squiggles1024/FitnessController/CAD Models/12mm-button-without-cap-with-round-square-cap-1.snapshot.3/12mmx12mm With White cap round.stp

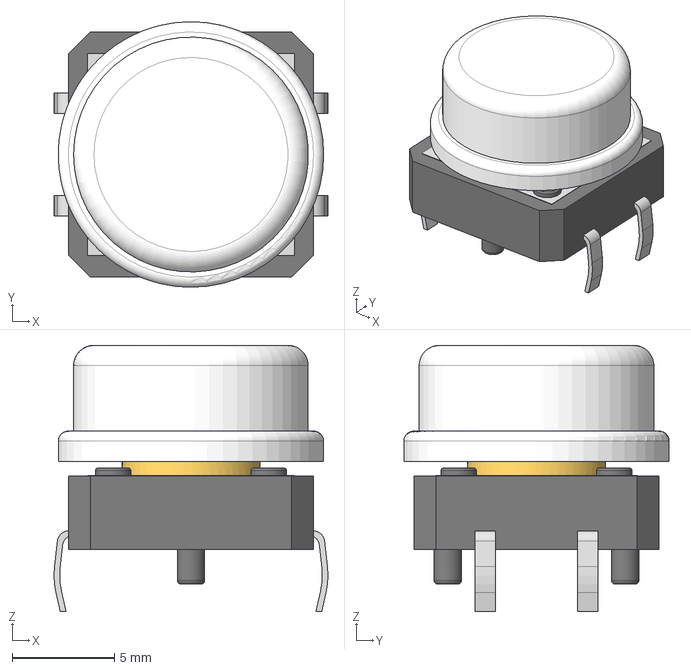
[picture p21: CAD file, 2022-12-01]
CAD Models/12mm-button-without-cap-with-round-square-cap-1.snapshot.3/12mmx12mm With White cap round.stp
13.4 x 13.0 x 13.0 mm
