squiggles1024/FitnessController/CAD Models/Trigger.SLDPRT

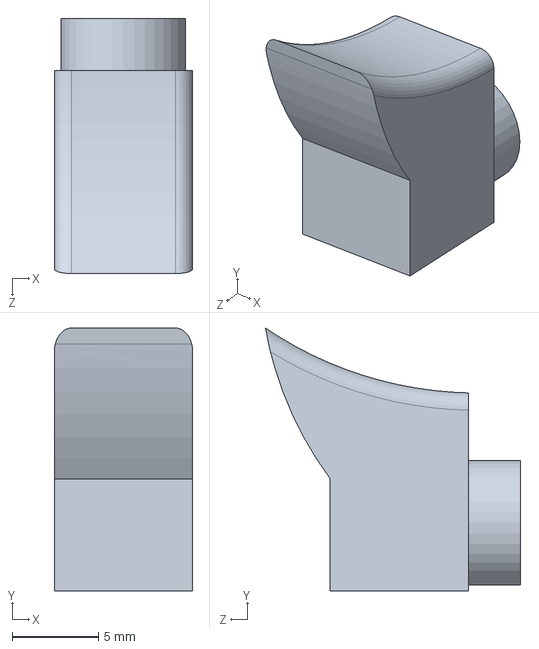
[picture p25: CAD file, 2022-12-01]
CAD Models/Trigger.SLDPRT
8.00 x 15.2 x 14.7 mm
