squiggles1024/FitnessController/CAD Models/NunChuck_Top.SLDPRT

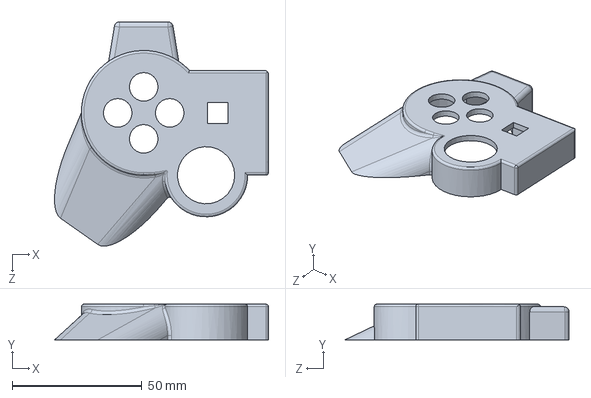
[picture p26: CAD file, 2022-12-01]
CAD Models/NunChuck_Top.SLDPRT
82.3 x 13.8 x 86.3 mm
