squiggles1024/FitnessController/CAD Models/12mm-button-without-cap-with-round-square-cap-1.snapshot.3/12mmx12mm Without cap.stp

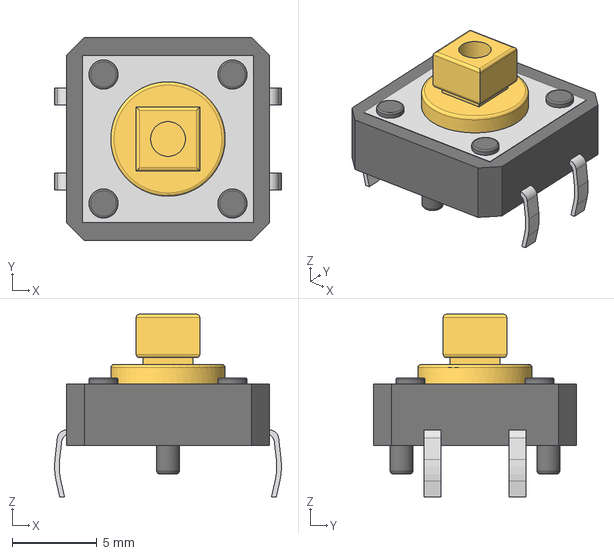
[picture p29: CAD file, 2022-12-01]
CAD Models/12mm-button-without-cap-with-round-square-cap-1.snapshot.3/12mmx12mm Without cap.stp
13.4 x 12.0 x 10.8 mm
