squiggles1024/FitnessController/CAD Models/tactile-switch-thru-6mm-series-1.snapshot.25/Tactal Switch -Thru (6mmx 6mmx4.5mm).stp

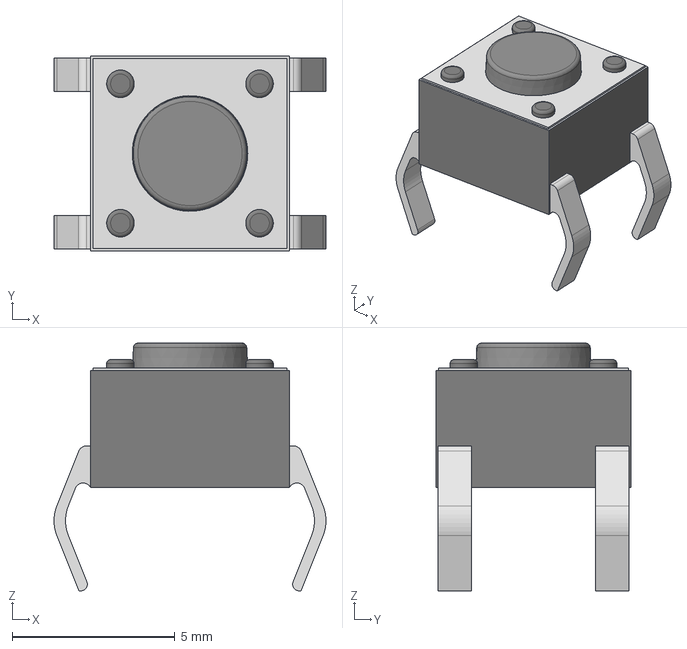
[picture p30: CAD file, 2022-12-01]
CAD Models/tactile-switch-thru-6mm-series-1.snapshot.25/Tactal Switch -Thru (6mmx 6mmx4.5mm).stp
8.37 x 5.99 x 7.62 mm
