squiggles1024/FitnessController/Core/Src/gpio.c

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

/* Includes ------------------------------------------------------------------*/
#include "gpio.h"

/*----------------------------------------------------------------------------*/
/* Configure GPIO                                                             */
/*----------------------------------------------------------------------------*/
/** Configure pins as
        * Analog
        * Input
        * Output
        * EVENT_OUT
        * EXTI
     PA9   ------> USB_OTG_FS_VBUS
     PA10   ------> USB_OTG_FS_ID
     PA11   ------> USB_OTG_FS_DM
     PA12   ------> USB_OTG_FS_DP
*/
void MX_GPIO_Init(void)
{

  GPIO_InitTypeDef GPIO_InitStruct = {0};

  /* GPIO Ports Clock Enable */
  __HAL_RCC_GPIOE_CLK_ENABLE();
  __HAL_RCC_GPIOC_CLK_ENABLE();
  __HAL_RCC_GPIOA_CLK_ENABLE();
  __HAL_RCC_GPIOB_CLK_ENABLE();
  __HAL_RCC_GPIOD_CLK_ENABLE();

  /*Configure GPIO pin Output Level */
  HAL_GPIO_WritePin(LED2_GPIO_Port, LED2_Pin, GPIO_PIN_RESET);

  /*Configure GPIO pin Output Level */
  HAL_GPIO_WritePin(SPBTLE_RF_SPI3_CSN_GPIO_Port, SPBTLE_RF_SPI3_CSN_Pin, GPIO_PIN_SET);

  /*Configure GPIO pin Output Level */
  HAL_GPIO_WritePin(LED3_WIFI__LED4_BLE_GPIO_Port, LED3_WIFI__LED4_BLE_Pin, GPIO_PIN_RESET);

  /*Configure GPIO pin Output Level */
  HAL_GPIO_WritePin(SPBTLE_RF_RST_GPIO_Port, SPBTLE_RF_RST_Pin, GPIO_PIN_RESET);

  /*Configure GPIO pin : PtPin */
  GPIO_InitStruct.Pin = SPBTLE_RF_IRQ_EXTI6_Pin;
  GPIO_InitStruct.Mode = GPIO_MODE_IT_RISING;
  GPIO_InitStruct.Pull = GPIO_NOPULL;
  HAL_GPIO_Init(SPBTLE_RF_IRQ_EXTI6_GPIO_Port, &GPIO_InitStruct);

  /*Configure GPIO pins : PAPin PAPin PAPin PAPin
                           PAPin PAPin PAPin PAPin */
  GPIO_InitStruct.Pin = XINPUT_GAMEPAD_B_Pin|XINPUT_GAMEPAD_A_Pin|XINPUT_GAMEPAD_DPAD_UP_Pin|XINPUT_GAMEPAD_START_Pin
                          |XINPUT_GAMEPAD_DPAD_RIGHT_Pin|XINPUT_GAMEPAD_DPAD_LEFT_Pin|XINPUT_GAMEPAD_DPAD_DOWN_Pin|XINPUT_GAMEPAD_RIGHT_SHOULDER_Pin;
  GPIO_InitStruct.Mode = GPIO_MODE_INPUT;
  GPIO_InitStruct.Pull = GPIO_PULLDOWN;
  HAL_GPIO_Init(GPIOA, &GPIO_InitStruct);

  /*Configure GPIO pin : PtPin */
  GPIO_InitStruct.Pin = XINPUT_GAMEPAD_RIGHT_THUMB_Pin;
  GPIO_InitStruct.Mode = GPIO_MODE_INPUT;
  GPIO_InitStruct.Pull = GPIO_PULLUP;
  HAL_GPIO_Init(XINPUT_GAMEPAD_RIGHT_THUMB_GPIO_Port, &GPIO_InitStruct);

  /*Configure GPIO pins : PBPin PBPin PBPin */
  GPIO_InitStruct.Pin = XINPUT_GAMEPAD_Y_Pin|XINPUT_GAMEPAD_LEFT_SHOULDER_Pin|XINPUT_GAMEPAD_BACK_Pin;
  GPIO_InitStruct.Mode = GPIO_MODE_INPUT;
  GPIO_InitStruct.Pull = GPIO_PULLDOWN;
  HAL_GPIO_Init(GPIOB, &GPIO_InitStruct);

  /*Configure GPIO pin : PtPin */
  GPIO_InitStruct.Pin = XINPUT_GAMEPAD_LEFT_THUMB_Pin;
  GPIO_InitStruct.Mode = GPIO_MODE_INPUT;
  GPIO_InitStruct.Pull = GPIO_PULLUP;
  HAL_GPIO_Init(XINPUT_GAMEPAD_LEFT_THUMB_GPIO_Port, &GPIO_InitStruct);

  /*Configure GPIO pin : PtPin */
  GPIO_InitStruct.Pin = LED2_Pin;
  GPIO_InitStruct.Mode = GPIO_MODE_OUTPUT_PP;
  GPIO_InitStruct.Pull = GPIO_NOPULL;
  GPIO_InitStruct.Speed = GPIO_SPEED_FREQ_LOW;
  HAL_GPIO_Init(LED2_GPIO_Port, &GPIO_InitStruct);

  /*Configure GPIO pin : PtPin */
  GPIO_InitStruct.Pin = SPBTLE_RF_SPI3_CSN_Pin;
  GPIO_InitStruct.Mode = GPIO_MODE_OUTPUT_PP;
  GPIO_InitStruct.Pull = GPIO_NOPULL;
  GPIO_InitStruct.Speed = GPIO_SPEED_FREQ_LOW;
  HAL_GPIO_Init(SPBTLE_RF_SPI3_CSN_GPIO_Port, &GPIO_InitStruct);

  /*Configure GPIO pin : PtPin */
  GPIO_InitStruct.Pin = XINPUT_GAMEPAD_X_Pin;
  GPIO_InitStruct.Mode = GPIO_MODE_INPUT;
  GPIO_InitStruct.Pull = GPIO_PULLDOWN;
  HAL_GPIO_Init(XINPUT_GAMEPAD_X_GPIO_Port, &GPIO_InitStruct);

  /*Configure GPIO pin : PtPin */
  GPIO_InitStruct.Pin = LED3_WIFI__LED4_BLE_Pin;
  GPIO_InitStruct.Mode = GPIO_MODE_OUTPUT_PP;
  GPIO_InitStruct.Pull = GPIO_NOPULL;
  GPIO_InitStruct.Speed = GPIO_SPEED_FREQ_LOW;
  HAL_GPIO_Init(LED3_WIFI__LED4_BLE_GPIO_Port, &GPIO_InitStruct);

  /*Configure GPIO pin : PtPin */
  GPIO_InitStruct.Pin = SPBTLE_RF_RST_Pin;
  GPIO_InitStruct.Mode = GPIO_MODE_OUTPUT_PP;
  GPIO_InitStruct.Pull = GPIO_NOPULL;
  GPIO_InitStruct.Speed = GPIO_SPEED_FREQ_LOW;
  HAL_GPIO_Init(SPBTLE_RF_RST_GPIO_Port, &GPIO_InitStruct);

  /*Configure GPIO pin : PtPin */
  GPIO_InitStruct.Pin = USB_OTG_FS_VBUS_Pin;
  GPIO_InitStruct.Mode = GPIO_MODE_INPUT;
  GPIO_InitStruct.Pull = GPIO_NOPULL;
  HAL_GPIO_Init(USB_OTG_FS_VBUS_GPIO_Port, &GPIO_InitStruct);

  /*Configure GPIO pins : PAPin PAPin PAPin */
  GPIO_InitStruct.Pin = USB_OTG_FS_ID_Pin|USB_OTG_FS_DM_Pin|USB_OTG_FS_DP_Pin;
  GPIO_InitStruct.Mode = GPIO_MODE_AF_PP;
  GPIO_InitStruct.Pull = GPIO_NOPULL;
  GPIO_InitStruct.Speed = GPIO_SPEED_FREQ_VERY_HIGH;
  GPIO_InitStruct.Alternate = GPIO_AF10_OTG_FS;
  HAL_GPIO_Init(GPIOA, &GPIO_InitStruct);

  /* EXTI interrupt init*/
  HAL_NVIC_SetPriority(EXTI9_5_IRQn, 0, 0);
  HAL_NVIC_EnableIRQ(EXTI9_5_IRQn);

}

/* USER CODE BEGIN 2 */
void BLE_GPIO_Init(void){
	  GPIO_InitTypeDef GPIO_InitStruct = {0};

	  /* GPIO Ports Clock Enable */
	  __HAL_RCC_GPIOE_CLK_ENABLE();
	  __HAL_RCC_GPIOC_CLK_ENABLE();
	  __HAL_RCC_GPIOA_CLK_ENABLE();
	  __HAL_RCC_GPIOB_CLK_ENABLE();
	  __HAL_RCC_GPIOD_CLK_ENABLE();

	  /*Configure GPIO pin Output Level */
	  HAL_GPIO_WritePin(LED2_GPIO_Port, LED2_Pin, GPIO_PIN_RESET);

	  /*Configure GPIO pin Output Level */
	  HAL_GPIO_WritePin(SPBTLE_RF_SPI3_CSN_GPIO_Port, SPBTLE_RF_SPI3_CSN_Pin, GPIO_PIN_SET);

	  /*Configure GPIO pin Output Level */
	  HAL_GPIO_WritePin(LED3_WIFI__LED4_BLE_GPIO_Port, LED3_WIFI__LED4_BLE_Pin, GPIO_PIN_RESET);

	  /*Configure GPIO pin Output Level */
	  HAL_GPIO_WritePin(SPBTLE_RF_RST_GPIO_Port, SPBTLE_RF_RST_Pin, GPIO_PIN_RESET);

	  /*Configure GPIO pin : PtPin */
	  GPIO_InitStruct.Pin = SPBTLE_RF_IRQ_EXTI6_Pin;
	  GPIO_InitStruct.Mode = GPIO_MODE_IT_RISING;
	  GPIO_InitStruct.Pull = GPIO_NOPULL;
	  HAL_GPIO_Init(SPBTLE_RF_IRQ_EXTI6_GPIO_Port, &GPIO_InitStruct);


	  /*Configure GPIO pin : PtPin */
	  GPIO_InitStruct.Pin = LED2_Pin;
	  GPIO_InitStruct.Mode = GPIO_MODE_OUTPUT_PP;
	  GPIO_InitStruct.Pull = GPIO_NOPULL;
	  GPIO_InitStruct.Speed = GPIO_SPEED_FREQ_LOW;
	  HAL_GPIO_Init(LED2_GPIO_Port, &GPIO_InitStruct);

	  /*Configure GPIO pin : PtPin */
	  GPIO_InitStruct.Pin = SPBTLE_RF_SPI3_CSN_Pin;
	  GPIO_InitStruct.Mode = GPIO_MODE_OUTPUT_PP;
	  GPIO_InitStruct.Pull = GPIO_NOPULL;
	  GPIO_InitStruct.Speed = GPIO_SPEED_FREQ_LOW;
	  HAL_GPIO_Init(SPBTLE_RF_SPI3_CSN_GPIO_Port, &GPIO_InitStruct);

	  GPIO_InitStruct.Pin = LED3_WIFI__LED4_BLE_Pin;
	  GPIO_InitStruct.Mode = GPIO_MODE_OUTPUT_PP;
	  GPIO_InitStruct.Pull = GPIO_NOPULL;
	  GPIO_InitStruct.Speed = GPIO_SPEED_FREQ_LOW;
	  HAL_GPIO_Init(LED3_WIFI__LED4_BLE_GPIO_Port, &GPIO_InitStruct);

	  /*Configure GPIO pin : PtPin */
	  GPIO_InitStruct.Pin = SPBTLE_RF_RST_Pin;
	  GPIO_InitStruct.Mode = GPIO_MODE_OUTPUT_PP;
	  GPIO_InitStruct.Pull = GPIO_NOPULL;
	  GPIO_InitStruct.Speed = GPIO_SPEED_FREQ_LOW;
	  HAL_GPIO_Init(SPBTLE_RF_RST_GPIO_Port, &GPIO_InitStruct);

	  /* EXTI interrupt init*/
	  HAL_NVIC_SetPriority(EXTI9_5_IRQn, 0, 0);
	  HAL_NVIC_EnableIRQ(EXTI9_5_IRQn);
}

void Button_GPIO_Init(void){
	  GPIO_InitTypeDef GPIO_InitStruct = {0};
	  /* GPIO Ports Clock Enable */
	  __HAL_RCC_GPIOE_CLK_ENABLE();
	  __HAL_RCC_GPIOC_CLK_ENABLE();
	  __HAL_RCC_GPIOA_CLK_ENABLE();
	  __HAL_RCC_GPIOB_CLK_ENABLE();
	  __HAL_RCC_GPIOD_CLK_ENABLE();


	  /*Configure GPIO pins : PAPin PAPin PAPin PAPin
	                           PAPin PAPin PAPin PAPin */
	  GPIO_InitStruct.Pin = XINPUT_GAMEPAD_B_Pin|XINPUT_GAMEPAD_A_Pin|XINPUT_GAMEPAD_DPAD_UP_Pin|XINPUT_GAMEPAD_START_Pin
	                          |XINPUT_GAMEPAD_DPAD_RIGHT_Pin|XINPUT_GAMEPAD_DPAD_LEFT_Pin|XINPUT_GAMEPAD_DPAD_DOWN_Pin|XINPUT_GAMEPAD_RIGHT_SHOULDER_Pin;
	  GPIO_InitStruct.Mode = GPIO_MODE_INPUT;
	  GPIO_InitStruct.Pull = GPIO_PULLDOWN;
	  HAL_GPIO_Init(GPIOA, &GPIO_InitStruct);

	  /*Configure GPIO pin : PtPin */
	  GPIO_InitStruct.Pin = XINPUT_GAMEPAD_RIGHT_THUMB_Pin;
	  GPIO_InitStruct.Mode = GPIO_MODE_INPUT;
	  GPIO_InitStruct.Pull = GPIO_PULLUP;
	  HAL_GPIO_Init(XINPUT_GAMEPAD_RIGHT_THUMB_GPIO_Port, &GPIO_InitStruct);

	  /*Configure GPIO pins : PBPin PBPin PBPin */
	  GPIO_InitStruct.Pin = XINPUT_GAMEPAD_Y_Pin|XINPUT_GAMEPAD_LEFT_SHOULDER_Pin|XINPUT_GAMEPAD_BACK_Pin;
	  GPIO_InitStruct.Mode = GPIO_MODE_INPUT;
	  GPIO_InitStruct.Pull = GPIO_PULLDOWN;
	  HAL_GPIO_Init(GPIOB, &GPIO_InitStruct);

	  /*Configure GPIO pin : PtPin */
	  GPIO_InitStruct.Pin = XINPUT_GAMEPAD_LEFT_THUMB_Pin;
	  GPIO_InitStruct.Mode = GPIO_MODE_INPUT;
	  GPIO_InitStruct.Pull = GPIO_PULLUP;
	  HAL_GPIO_Init(XINPUT_GAMEPAD_LEFT_THUMB_GPIO_Port, &GPIO_InitStruct);

	  /*Configure GPIO pin : PtPin */
	  GPIO_InitStruct.Pin = XINPUT_GAMEPAD_X_Pin;
	  GPIO_InitStruct.Mode = GPIO_MODE_INPUT;
	  GPIO_InitStruct.Pull = GPIO_PULLDOWN;
	  HAL_GPIO_Init(XINPUT_GAMEPAD_X_GPIO_Port, &GPIO_InitStruct);

}

void ADC_GPIO_Init(void){
	  __HAL_RCC_GPIOC_CLK_ENABLE();
}

void MAX30102_GPIO_Init(){
	  __HAL_RCC_GPIOB_CLK_ENABLE();
}
/* USER CODE END 2 */
