squiggles1024/FitnessController/Core/Src/adc.c

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
/* Includes ------------------------------------------------------------------*/
#include "adc.h"

ADC_HandleTypeDef hadc1;
DMA_HandleTypeDef hdma_adc1;

/* ADC1 init function */
void MX_ADC1_Init(void)
{

  ADC_MultiModeTypeDef multimode = {0};
  ADC_ChannelConfTypeDef sConfig = {0};

  /** Common config
  */
  hadc1.Instance = ADC1;
  hadc1.Init.ClockPrescaler = ADC_CLOCK_ASYNC_DIV1;
  hadc1.Init.Resolution = ADC_RESOLUTION_12B;
  hadc1.Init.DataAlign = ADC_DATAALIGN_RIGHT;
  hadc1.Init.ScanConvMode = ADC_SCAN_ENABLE;
  hadc1.Init.EOCSelection = ADC_EOC_SINGLE_CONV;
  hadc1.Init.LowPowerAutoWait = DISABLE;
  hadc1.Init.ContinuousConvMode = ENABLE;
  hadc1.Init.NbrOfConversion = 6;
  hadc1.Init.DiscontinuousConvMode = DISABLE;
  hadc1.Init.ExternalTrigConv = ADC_SOFTWARE_START;
  hadc1.Init.ExternalTrigConvEdge = ADC_EXTERNALTRIGCONVEDGE_NONE;
  hadc1.Init.DMAContinuousRequests = ENABLE;
  hadc1.Init.Overrun = ADC_OVR_DATA_PRESERVED;
  hadc1.Init.OversamplingMode = DISABLE;
  if (HAL_ADC_Init(&hadc1) != HAL_OK)
  {
    Error_Handler();
  }

  /** Configure the ADC multi-mode
  */
  multimode.Mode = ADC_MODE_INDEPENDENT;
  if (HAL_ADCEx_MultiModeConfigChannel(&hadc1, &multimode) != HAL_OK)
  {
    Error_Handler();
  }

  /** Configure Regular Channel
  */
  sConfig.Channel = ADC_CHANNEL_1;
  sConfig.Rank = ADC_REGULAR_RANK_1;
  sConfig.SamplingTime = ADC_SAMPLETIME_47CYCLES_5;
  sConfig.SingleDiff = ADC_SINGLE_ENDED;
  sConfig.OffsetNumber = ADC_OFFSET_NONE;
  sConfig.Offset = 0;
  if (HAL_ADC_ConfigChannel(&hadc1, &sConfig) != HAL_OK)
  {
    Error_Handler();
  }

  /** Configure Regular Channel
  */
  sConfig.Channel = ADC_CHANNEL_2;
  sConfig.Rank = ADC_REGULAR_RANK_2;
  if (HAL_ADC_ConfigChannel(&hadc1, &sConfig) != HAL_OK)
  {
    Error_Handler();
  }

  /** Configure Regular Channel
  */
  sConfig.Channel = ADC_CHANNEL_3;
  sConfig.Rank = ADC_REGULAR_RANK_3;
  if (HAL_ADC_ConfigChannel(&hadc1, &sConfig) != HAL_OK)
  {
    Error_Handler();
  }

  /** Configure Regular Channel
  */
  sConfig.Channel = ADC_CHANNEL_4;
  sConfig.Rank = ADC_REGULAR_RANK_4;
  if (HAL_ADC_ConfigChannel(&hadc1, &sConfig) != HAL_OK)
  {
    Error_Handler();
  }

  /** Configure Regular Channel
  */
  sConfig.Channel = ADC_CHANNEL_13;
  sConfig.Rank = ADC_REGULAR_RANK_5;
  if (HAL_ADC_ConfigChannel(&hadc1, &sConfig) != HAL_OK)
  {
    Error_Handler();
  }

  /** Configure Regular Channel
  */
  sConfig.Channel = ADC_CHANNEL_14;
  sConfig.Rank = ADC_REGULAR_RANK_6;
  if (HAL_ADC_ConfigChannel(&hadc1, &sConfig) != HAL_OK)
  {
    Error_Handler();
  }
}

void HAL_ADC_MspInit(ADC_HandleTypeDef* adcHandle)
{

  GPIO_InitTypeDef GPIO_InitStruct = {0};
  RCC_PeriphCLKInitTypeDef PeriphClkInit = {0};
  if(adcHandle->Instance==ADC1)
  {
  /** Initializes the peripherals clock
  */
    PeriphClkInit.PeriphClockSelection = RCC_PERIPHCLK_ADC;
    PeriphClkInit.AdcClockSelection = RCC_ADCCLKSOURCE_PLLSAI1;
    PeriphClkInit.PLLSAI1.PLLSAI1Source = RCC_PLLSOURCE_MSI;
    PeriphClkInit.PLLSAI1.PLLSAI1M = 1;
    PeriphClkInit.PLLSAI1.PLLSAI1N = 24;
    PeriphClkInit.PLLSAI1.PLLSAI1P = RCC_PLLP_DIV7;
    PeriphClkInit.PLLSAI1.PLLSAI1Q = RCC_PLLQ_DIV2;
    PeriphClkInit.PLLSAI1.PLLSAI1R = RCC_PLLR_DIV2;
    PeriphClkInit.PLLSAI1.PLLSAI1ClockOut = RCC_PLLSAI1_ADC1CLK;
    if (HAL_RCCEx_PeriphCLKConfig(&PeriphClkInit) != HAL_OK)
    {
      Error_Handler();
    }

    /* ADC1 clock enable */
    __HAL_RCC_ADC_CLK_ENABLE();

    __HAL_RCC_GPIOC_CLK_ENABLE();
    /**ADC1 GPIO Configuration
    PC0     ------> ADC1_IN1
    PC1     ------> ADC1_IN2
    PC2     ------> ADC1_IN3
    PC3     ------> ADC1_IN4
    PC4     ------> ADC1_IN13
    PC5     ------> ADC1_IN14
    */
    GPIO_InitStruct.Pin = LeftStick_X_Pin|LeftStick_Y_Pin|RightStick_X_Pin|RightStick_Y_Pin
                          |LeftTrigger_Pin|RightTrigger_Pin;
    GPIO_InitStruct.Mode = GPIO_MODE_ANALOG_ADC_CONTROL;
    GPIO_InitStruct.Pull = GPIO_NOPULL;
    HAL_GPIO_Init(GPIOC, &GPIO_InitStruct);

    /* ADC1 DMA Init */
    /* ADC1 Init */
    hdma_adc1.Instance = DMA1_Channel1;
    hdma_adc1.Init.Request = DMA_REQUEST_0;
    hdma_adc1.Init.Direction = DMA_PERIPH_TO_MEMORY;
    hdma_adc1.Init.PeriphInc = DMA_PINC_DISABLE;
    hdma_adc1.Init.MemInc = DMA_MINC_ENABLE;
    hdma_adc1.Init.PeriphDataAlignment = DMA_PDATAALIGN_HALFWORD;
    hdma_adc1.Init.MemDataAlignment = DMA_MDATAALIGN_HALFWORD;
    hdma_adc1.Init.Mode = DMA_CIRCULAR;
    hdma_adc1.Init.Priority = DMA_PRIORITY_LOW;
    if (HAL_DMA_Init(&hdma_adc1) != HAL_OK)
    {
      Error_Handler();
    }

    __HAL_LINKDMA(adcHandle,DMA_Handle,hdma_adc1);

  }
}

void HAL_ADC_MspDeInit(ADC_HandleTypeDef* adcHandle)
{

  if(adcHandle->Instance==ADC1)
  {
    /* Peripheral clock disable */
    __HAL_RCC_ADC_CLK_DISABLE();

    /**ADC1 GPIO Configuration
    PC0     ------> ADC1_IN1
    PC1     ------> ADC1_IN2
    PC2     ------> ADC1_IN3
    PC3     ------> ADC1_IN4
    PC4     ------> ADC1_IN13
    PC5     ------> ADC1_IN14
    */
    HAL_GPIO_DeInit(GPIOC, LeftStick_X_Pin|LeftStick_Y_Pin|RightStick_X_Pin|RightStick_Y_Pin
                          |LeftTrigger_Pin|RightTrigger_Pin);

    /* ADC1 DMA DeInit */
    HAL_DMA_DeInit(adcHandle->DMA_Handle);
  }
}

/* USER CODE BEGIN 1 */
void ADC1_Init(){
	  ADC_MultiModeTypeDef multimode = {0};
	  ADC_ChannelConfTypeDef sConfig = {0};

	  hadc1.Instance = ADC1;
	  hadc1.Init.ClockPrescaler = ADC_CLOCK_ASYNC_DIV1;
	  hadc1.Init.Resolution = ADC_RESOLUTION_12B;
	  hadc1.Init.DataAlign = ADC_DATAALIGN_RIGHT;
	  hadc1.Init.ScanConvMode = ADC_SCAN_ENABLE;
	  hadc1.Init.EOCSelection = ADC_EOC_SINGLE_CONV;
	  hadc1.Init.LowPowerAutoWait = DISABLE;
	  hadc1.Init.ContinuousConvMode = ENABLE;
	  hadc1.Init.NbrOfConversion = 6;
	  hadc1.Init.DiscontinuousConvMode = DISABLE;
	  hadc1.Init.ExternalTrigConv = ADC_SOFTWARE_START;
	  hadc1.Init.ExternalTrigConvEdge = ADC_EXTERNALTRIGCONVEDGE_NONE;
	  hadc1.Init.DMAContinuousRequests = ENABLE;
	  hadc1.Init.Overrun = ADC_OVR_DATA_PRESERVED;
	  hadc1.Init.OversamplingMode = DISABLE;
	  if (HAL_ADC_Init(&hadc1) != HAL_OK)
	  {
	    Error_Handler();
	  }

	  /** Configure the ADC multi-mode
	  */
	  multimode.Mode = ADC_MODE_INDEPENDENT;
	  if (HAL_ADCEx_MultiModeConfigChannel(&hadc1, &multimode) != HAL_OK)
	  {
	    Error_Handler();
	  }

	  /** Configure Regular Channel
	  */
	  sConfig.Channel = ADC_CHANNEL_1;
	  sConfig.Rank = ADC_REGULAR_RANK_1;
	  sConfig.SamplingTime = ADC_SAMPLETIME_47CYCLES_5;
	  sConfig.SingleDiff = ADC_SINGLE_ENDED;
	  sConfig.OffsetNumber = ADC_OFFSET_NONE;
	  sConfig.Offset = 0;
	  if (HAL_ADC_ConfigChannel(&hadc1, &sConfig) != HAL_OK)
	  {
	    Error_Handler();
	  }

	  /** Configure Regular Channel
	  */
	  sConfig.Channel = ADC_CHANNEL_2;
	  sConfig.Rank = ADC_REGULAR_RANK_2;
	  if (HAL_ADC_ConfigChannel(&hadc1, &sConfig) != HAL_OK)
	  {
	    Error_Handler();
	  }

	  /** Configure Regular Channel
	  */
	  sConfig.Channel = ADC_CHANNEL_3;
	  sConfig.Rank = ADC_REGULAR_RANK_3;
	  if (HAL_ADC_ConfigChannel(&hadc1, &sConfig) != HAL_OK)
	  {
	    Error_Handler();
	  }

	  /** Configure Regular Channel
	  */
	  sConfig.Channel = ADC_CHANNEL_4;
	  sConfig.Rank = ADC_REGULAR_RANK_4;
	  if (HAL_ADC_ConfigChannel(&hadc1, &sConfig) != HAL_OK)
	  {
	    Error_Handler();
	  }

	  /** Configure Regular Channel
	  */
	  sConfig.Channel = ADC_CHANNEL_13;
	  sConfig.Rank = ADC_REGULAR_RANK_5;
	  if (HAL_ADC_ConfigChannel(&hadc1, &sConfig) != HAL_OK)
	  {
	    Error_Handler();
	  }

	  /** Configure Regular Channel
	  */
	  sConfig.Channel = ADC_CHANNEL_14;
	  sConfig.Rank = ADC_REGULAR_RANK_6;
	  if (HAL_ADC_ConfigChannel(&hadc1, &sConfig) != HAL_OK)
	  {
	    Error_Handler();
	  }
}

volatile uint16_t adc_buffer[6];
uint8_t ADC_Init_Status = ADC_UNINITIALIZED;
/* USER CODE END 1 */
